splitkb/Zenestra/zenestra-template/zenestra-template.kicad_sch

## KiCad design zenestra-template/zenestra-template.kicad_sch (2023-07-24)

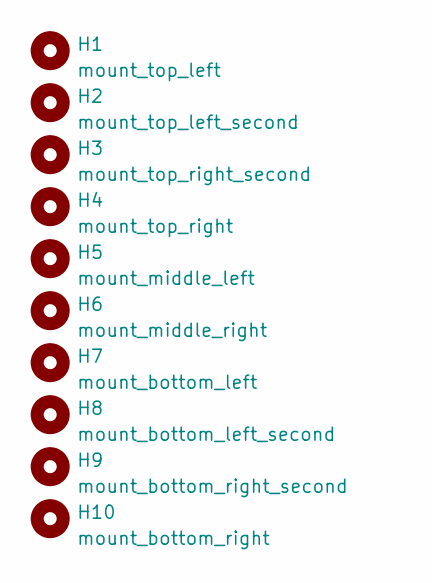
[picture p9: schematic zenestra-template.kicad_sch]

Parts:
H1: mount_top_left; MountingHole_3.2mm_M3_DIN965_Pad
H2: mount_top_left_second; MountingHole_3.2mm_M3_DIN965_Pad
H3: mount_top_right_second; MountingHole_3.2mm_M3_DIN965_Pad
H4: mount_top_right; MountingHole_3.2mm_M3_DIN965_Pad
H5: mount_middle_left; MountingHole_3.2mm_M3_DIN965_Pad
H6: mount_middle_right; MountingHole_3.2mm_M3_DIN965_Pad
H7: mount_bottom_left; MountingHole_3.2mm_M3_DIN965_Pad
H8: mount_bottom_left_second; MountingHole_3.2mm_M3_DIN965_Pad
H9: mount_bottom_right_second; MountingHole_3.2mm_M3_DIN965_Pad
H10: mount_bottom_right; MountingHole_3.2mm_M3_DIN965_Pad
